mumrah/ninotnc-ble/firmware/oled.c

#include <stdio.h>
#include <string.h>
#include <stdlib.h>
#include <ctype.h>
#include "pico/stdlib.h"
#include "pico/binary_info.h"
#include "hardware/i2c.h"

#include "ssd1306_font.h"
#include "config.h"
#include "oled.h"

#define SSD1306_I2C_ADDR            _u(0x3C)

#ifndef SSD1306_ROT
  #define SSD1306_ROT 0
#endif 

// 400 is usual, but often these can be overclocked to improve display response.
// Tested at 1000 on both 32 and 84 pixel height devices and it worked.
#define SSD1306_I2C_CLK             400
//#define SSD1306_I2C_CLK             1000


// commands (see datasheet)
#define SSD1306_SET_MEM_MODE        _u(0x20)
#define SSD1306_SET_COL_ADDR        _u(0x21)
#define SSD1306_SET_PAGE_ADDR       _u(0x22)
#define SSD1306_SET_HORIZ_SCROLL    _u(0x26)
#define SSD1306_SET_SCROLL          _u(0x2E)

#define SSD1306_SET_DISP_START_LINE _u(0x40)

#define SSD1306_SET_CONTRAST        _u(0x81)
#define SSD1306_SET_CHARGE_PUMP     _u(0x8D)

#define SSD1306_SET_SEG_REMAP       _u(0xA0)
#define SSD1306_SET_ENTIRE_ON       _u(0xA4)
#define SSD1306_SET_ALL_ON          _u(0xA5)
#define SSD1306_SET_NORM_DISP       _u(0xA6)
#define SSD1306_SET_INV_DISP        _u(0xA7)
#define SSD1306_SET_MUX_RATIO       _u(0xA8)
#define SSD1306_SET_DISP            _u(0xAE)
#define SSD1306_SET_COM_OUT_DIR     _u(0xC0)
#define SSD1306_SET_COM_OUT_DIR_FLIP _u(0xC0)

#define SSD1306_SET_DISP_OFFSET     _u(0xD3)
#define SSD1306_SET_DISP_CLK_DIV    _u(0xD5)
#define SSD1306_SET_PRECHARGE       _u(0xD9)
#define SSD1306_SET_COM_PIN_CFG     _u(0xDA)
#define SSD1306_SET_VCOM_DESEL      _u(0xDB)

#define SSD1306_WRITE_MODE         _u(0xFE)
#define SSD1306_READ_MODE          _u(0xFF)

static void SSD1306_send_cmd(uint8_t cmd) {
    // I2C write process expects a control byte followed by data
    // this "data" can be a command or data to follow up a command
    // Co = 1, D/C = 0 => the driver expects a command
    uint8_t buf[2] = {0x80, cmd};
    i2c_write_blocking(i2c_default, SSD1306_I2C_ADDR, buf, 2, false);
}

static void SSD1306_send_cmd_list(uint8_t *buf, int num) {
    for (int i=0;i<num;i++)
        SSD1306_send_cmd(buf[i]);
}

static void SSD1306_send_buf(uint8_t buf[], int buflen) {
    // in horizontal addressing mode, the column address pointer auto-increments
    // and then wraps around to the next page, so we can send the entire frame
    // buffer in one gooooooo!

    // copy our frame buffer into a new buffer because we need to add the control byte
    // to the beginning

    uint8_t *temp_buf = malloc(buflen + 1);

    temp_buf[0] = 0x40;
    memcpy(temp_buf+1, buf, buflen);

    i2c_write_blocking(i2c_default, SSD1306_I2C_ADDR, temp_buf, buflen + 1, false);

    free(temp_buf);
}

// Rotation 0:  SSD1306_SET_SEG_REMAP | 0x01, SSD1306_SET_COM_OUT_DIR | 0x08
// Rotation 180: SSD1306_SET_SEG_REMAP, SSD1306_SET_COM_OUT_DIR
static void SSD1306_Init() {
    // Setup the SSD1306
    uint8_t cmds[] = {
        SSD1306_SET_DISP,               // set display off
        /* memory mapping */
        SSD1306_SET_MEM_MODE,           // set memory address mode 0 = horizontal, 1 = vertical, 2 = page
        0x00,                           // horizontal addressing mode
        /* resolution and layout */
        SSD1306_SET_DISP_START_LINE,    // set display start line to 0
        //SSD1306_SET_SEG_REMAP | 0x01,   // set segment re-map, column address 127 is mapped to SEG0
#if (SSD1306_ROT == 0)
        SSD1306_SET_SEG_REMAP | 0x01,          // set segment re-map, column address 127 is mapped to SEG0
#else
        SSD1306_SET_SEG_REMAP,          // set segment re-map, column address 127 is mapped to SEG0
#endif
        SSD1306_SET_MUX_RATIO,          // set multiplex ratio
        SSD1306_HEIGHT - 1,             // Display height - 1
#if (SSD1306_ROT == 0) 
        SSD1306_SET_COM_OUT_DIR | 0x08, // set COM (common) output scan direction. Scan from bottom up, COM[N-1] to COM0
#else
        SSD1306_SET_COM_OUT_DIR,
#endif
        SSD1306_SET_DISP_OFFSET,        // set display offset
        0x00,                           // no offset
        SSD1306_SET_COM_PIN_CFG,        // set COM (common) pins hardware configuration. Board specific magic number.
                                        // 0x02 Works for 128x32, 0x12 Possibly works for 128x64. Other options 0x22, 0x32
#if ((SSD1306_WIDTH == 128) && (SSD1306_HEIGHT == 32))
        0x02,
#elif ((SSD1306_WIDTH == 128) && (SSD1306_HEIGHT == 64))
        0x12,
#else
        0x02,
#endif
        /* timing and driving scheme */
        SSD1306_SET_DISP_CLK_DIV,       // set display clock divide ratio
        0x80,                           // div ratio of 1, standard freq
        SSD1306_SET_PRECHARGE,          // set pre-charge period
        0xF1,                           // Vcc internally generated on our board
        SSD1306_SET_VCOM_DESEL,         // set VCOMH deselect level
        0x30,                           // 0.83xVcc
        /* display */
        SSD1306_SET_CONTRAST,           // set contrast control
        0xFF,
        SSD1306_SET_ENTIRE_ON,          // set entire display on to follow RAM content
        SSD1306_SET_NORM_DISP,           // set normal (not inverted) display
        SSD1306_SET_CHARGE_PUMP,        // set charge pump
        0x14,                           // Vcc internally generated on our board
        SSD1306_SET_SCROLL | 0x00,      // deactivate horizontal scrolling if set. This is necessary as memory writes will corrupt if scrolling was enabled
        SSD1306_SET_DISP | 0x01, // turn display on
    };
    SSD1306_send_cmd_list(cmds, count_of(cmds));
}




static uint8_t * font = font_tiny_8_8;
const uint8_t font_h = 8;
const uint8_t font_w = 8;


static inline int GetFontIndex(uint8_t ch) {
    if (ch < 32) {
        return 31; // ?
    } else if (ch > 126) {
        return 0;
    } else {
        return ch - 32;
    }
}

static void WriteChar(uint8_t *buf, int16_t x, int16_t y, uint8_t ch) {
    if (x > SSD1306_WIDTH - font_w || y > SSD1306_HEIGHT - font_h)
        return;

    // For the moment, only write on Y row boundaries (every 8 vertical pixels)
    y = y/font_h;

    int idx = GetFontIndex(ch);
    int fb_idx = y * 128 + x;

    for (int i=0;i<font_w;i++) {
        buf[fb_idx++] = font[idx * font_h + i];
    }
}

static void WriteString(uint8_t *buf, int16_t x, int16_t y, char *str) {
    // Cull out any string off the screen
    if (x > SSD1306_WIDTH - 8 || y > SSD1306_HEIGHT - 8)
        return;

    while (*str) {
        WriteChar(buf, x, y, *str++);
        x+=8;
    }
}

static void render(OLED * oled) {
    // update a portion of the display with a render area
    uint8_t cmds[] = {
        SSD1306_SET_COL_ADDR,
        oled->start_col,
        oled->end_col,
        SSD1306_SET_PAGE_ADDR,
        oled->start_page,
        oled->end_page
    };

    SSD1306_send_cmd_list(cmds, count_of(cmds));
    SSD1306_send_buf(oled->buffer, oled->render_buflen);
}

void oled_init(OLED * oled) {
    // Setup i2c
    i2c_init(i2c_default, SSD1306_I2C_CLK * 1000);
    gpio_set_function(PICO_DEFAULT_I2C_SDA_PIN, GPIO_FUNC_I2C);
    gpio_set_function(PICO_DEFAULT_I2C_SCL_PIN, GPIO_FUNC_I2C);
    gpio_pull_up(PICO_DEFAULT_I2C_SDA_PIN);
    gpio_pull_up(PICO_DEFAULT_I2C_SCL_PIN);

    // Setup the SSD1306
    SSD1306_Init();

    // Setup our struct
    oled->start_col = 0;
    oled->end_col = SSD1306_WIDTH - 1;
    oled->start_page = 0;
    oled->end_page = SSD1306_NUM_PAGES - 1;
    oled->render_buflen = (oled->end_col - oled->start_col + 1) * (oled->end_page - oled->start_page + 1);
}

void oled_deinit(OLED * oled) {
    oled_clear(oled);
    sleep_ms(50);
    i2c_deinit(i2c_default);
}

void oled_clear(OLED * oled) {
    memset(oled->buffer, 0, SSD1306_BUF_LEN);
    render(oled);
}

void oled_write_char(OLED * oled, int16_t x, int16_t y, char ch) {
   WriteChar(oled->buffer, x, y, ch);
}

void oled_write_string(OLED * oled, int16_t x, int16_t y, char * str) {
   WriteString(oled->buffer, x, y, str);
}

void oled_render(OLED * oled) {
    render(oled);
}
